ozseccon/ozseccon2019_badge/hw/ozseccon_2019/Badge_2019/gerbers/Production/Validate/prototype-F.SilkS.pdf

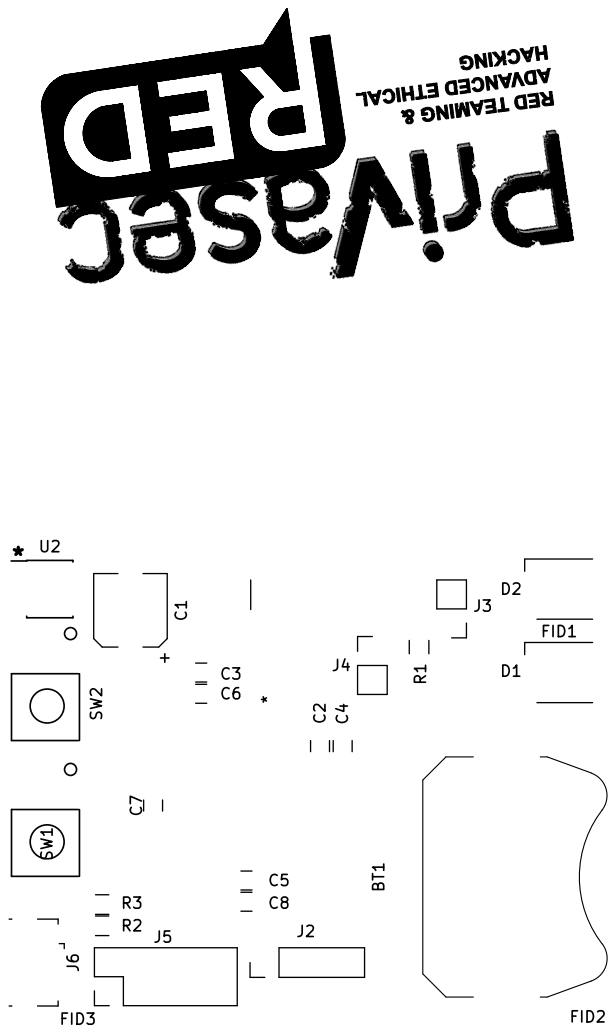
[picture p12: page 1]
