ozseccon/ozseccon2019_badge/hw/ozseccon_2019/Badge_2019/gerbers/Production/Validate/prototype.pdf

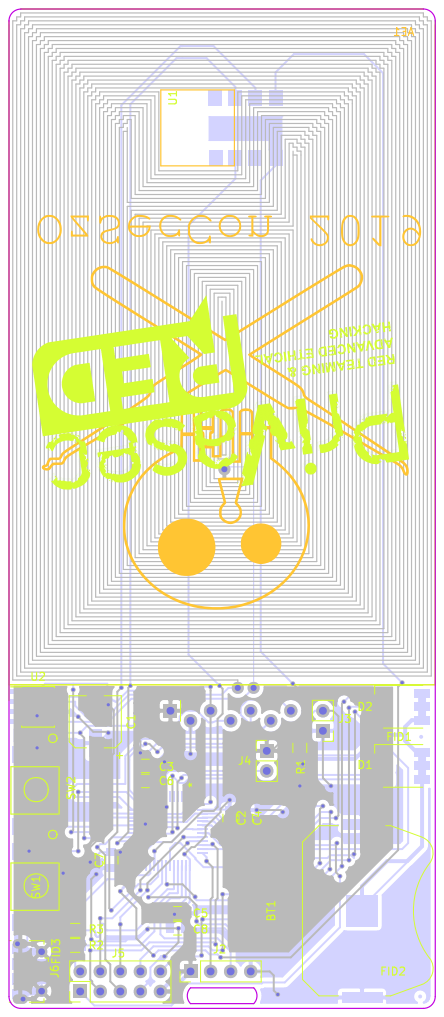
[picture p13: page 1]
