ozseccon/ozseccon2019_badge/hw/ozseccon_2019/Badge_2019/gerbers/Production/Validate/validate.pdf

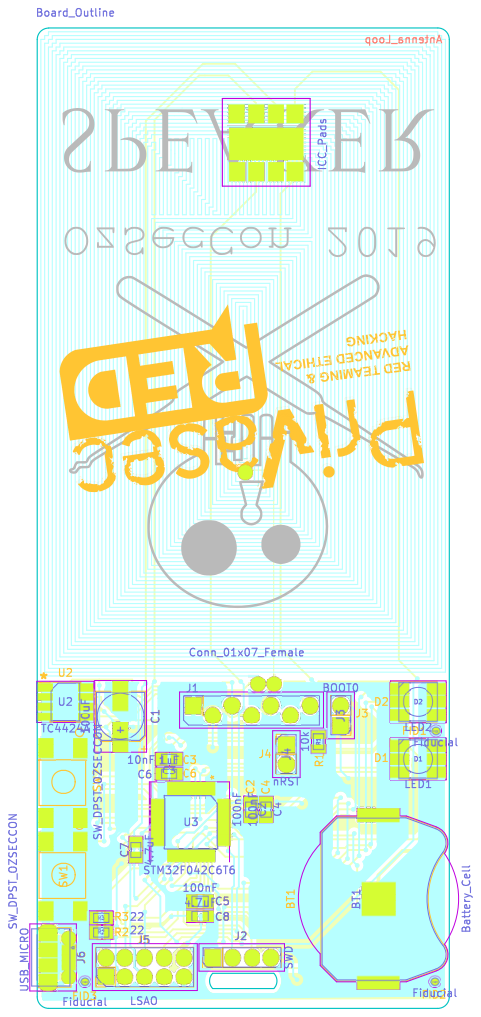
[picture p14: page 1]
