ozseccon/ozseccon2019_badge/hw/ozseccon_2019/Badge_2019/gerbers/svgs/prototype-Edge.Cuts.pdf

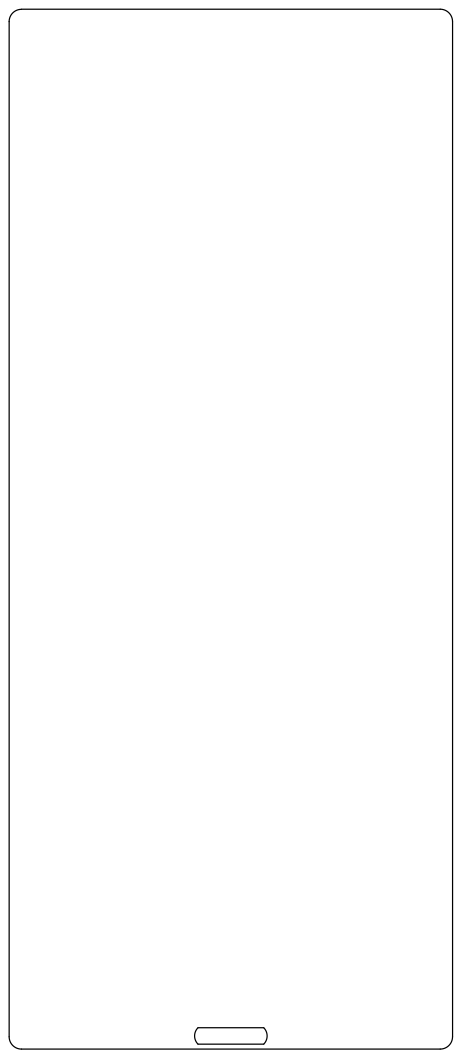
[picture p15: page 1]
