ozseccon/ozseccon2019_badge/hw/ozseccon_2019/Badge_2019/gerbers/svgs/prototype-F.Cu.pdf

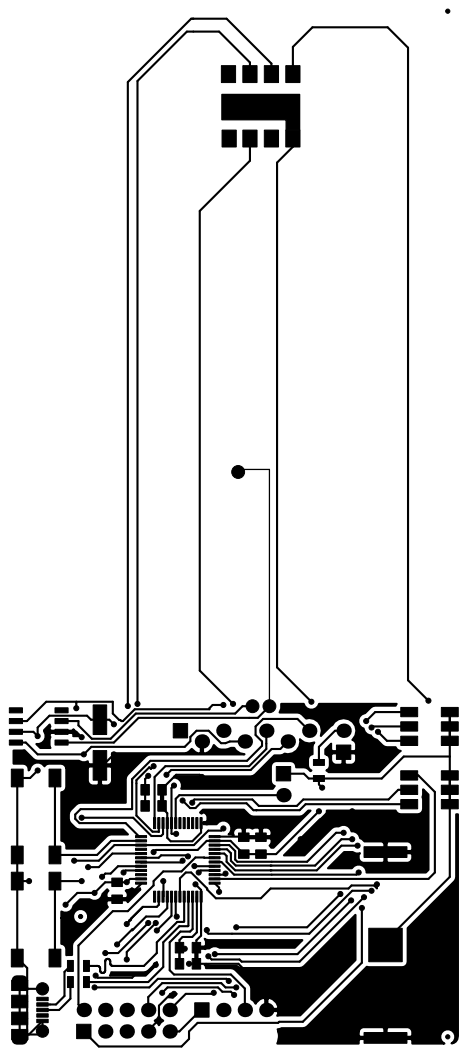
[picture p16: page 1]
