ozseccon/ozseccon2019_badge/hw/ozseccon_2019/Badge_2019/gerbers/svgs/prototype-F.Mask.pdf

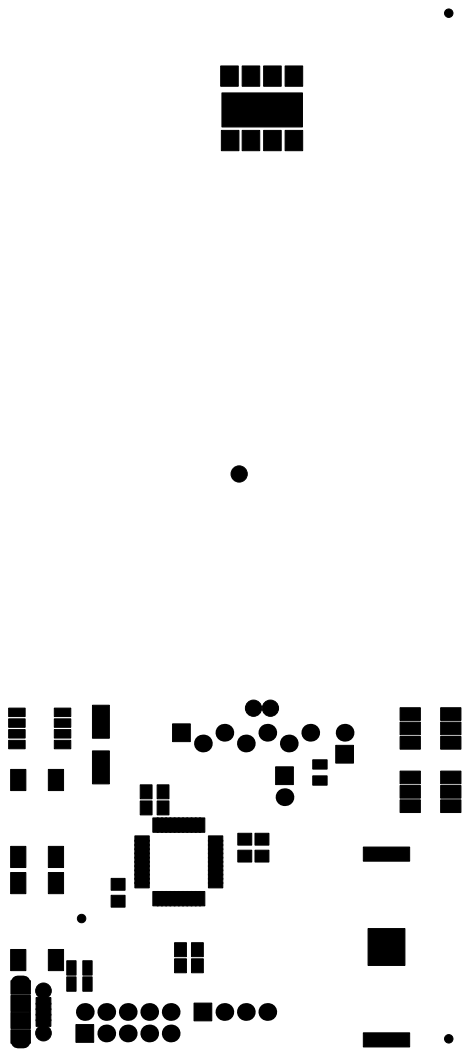
[picture p17: page 1]
