ozseccon/ozseccon2019_badge/hw/ozseccon_2019/Badge_2019/gerbers/svgs/prototype-F.SilkS.pdf

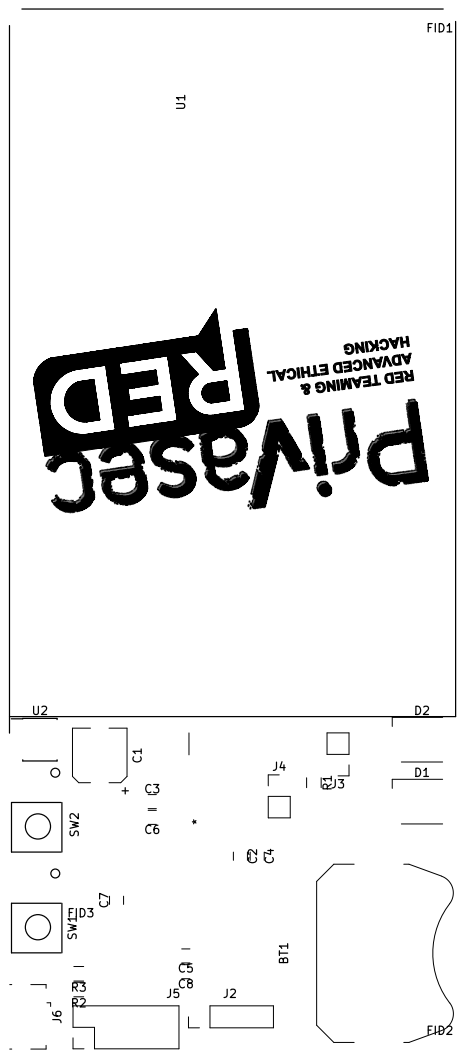
[picture p18: page 1]
