ozseccon/ozseccon2019_badge/hw/ozseccon_2019/Badge_2019/gerbers/Production/Validate/prototype-B.Cu.pdf

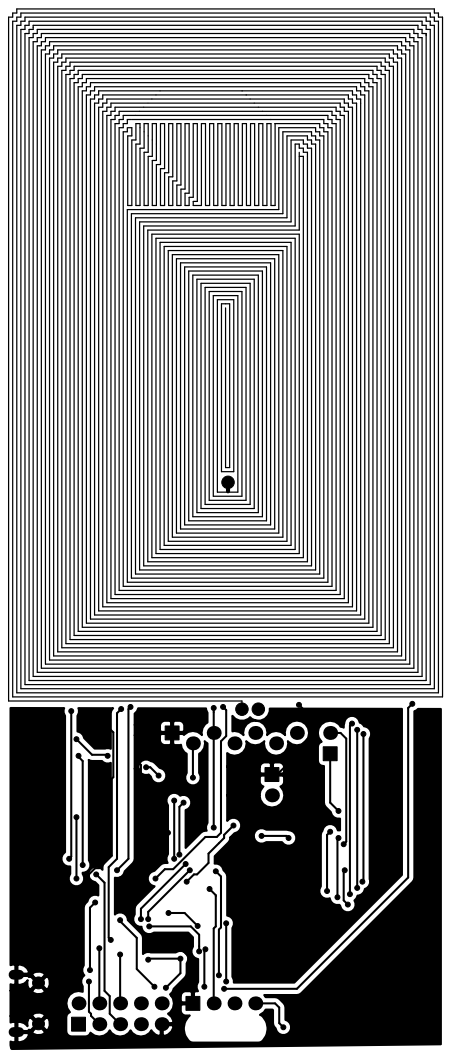
[picture p19: page 1]
