ozseccon/ozseccon2019_badge/hw/ozseccon_2019/Badge_2019/gerbers/Production/Validate/prototype-B.Mask.pdf

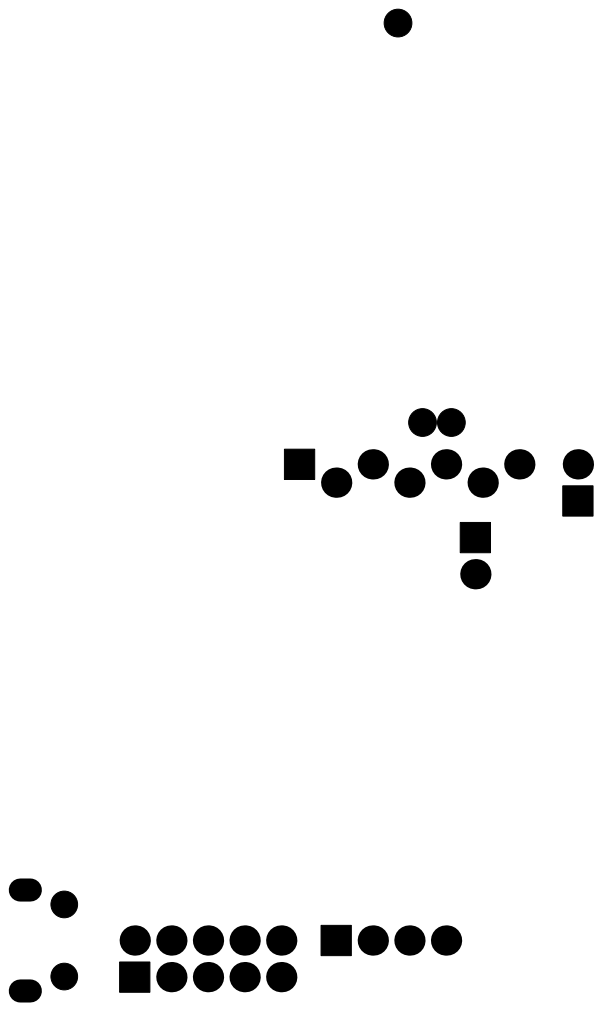
[picture p20: page 1]
