ozseccon/ozseccon2019_badge/hw/ozseccon_2019/Badge_2019/gerbers/Production/Validate/prototype-B.SilkS.pdf

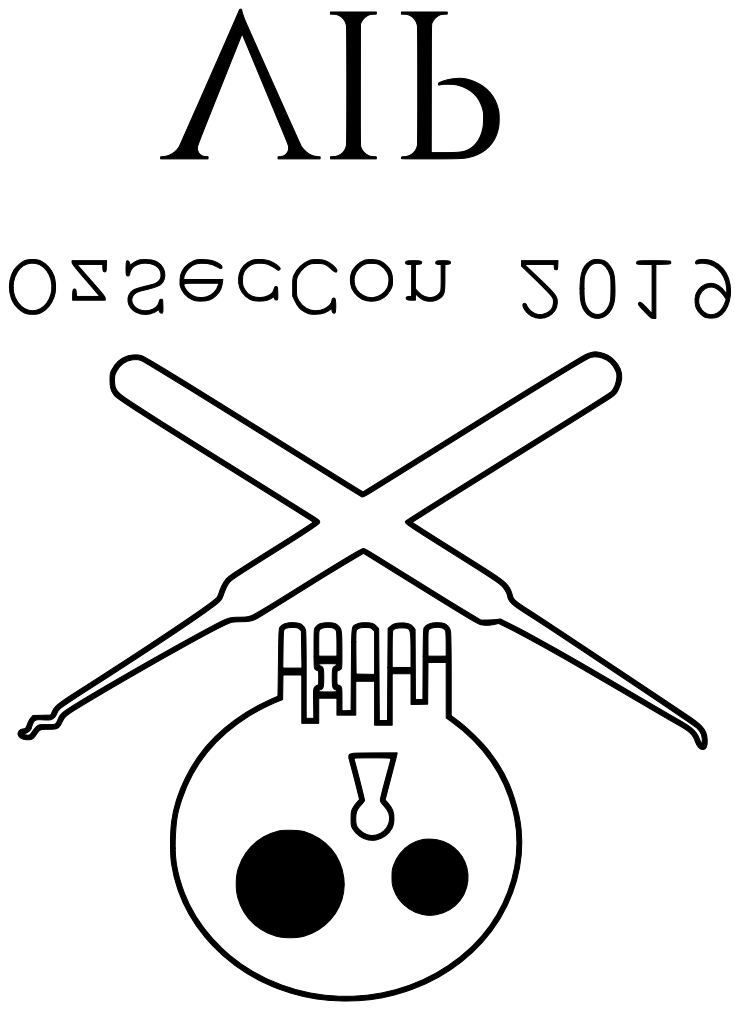
[picture p21: page 1]
