ozseccon/ozseccon2019_badge/hw/ozseccon_2019/Badge_2019/gerbers/svgs/prototype-B.Cu.pdf

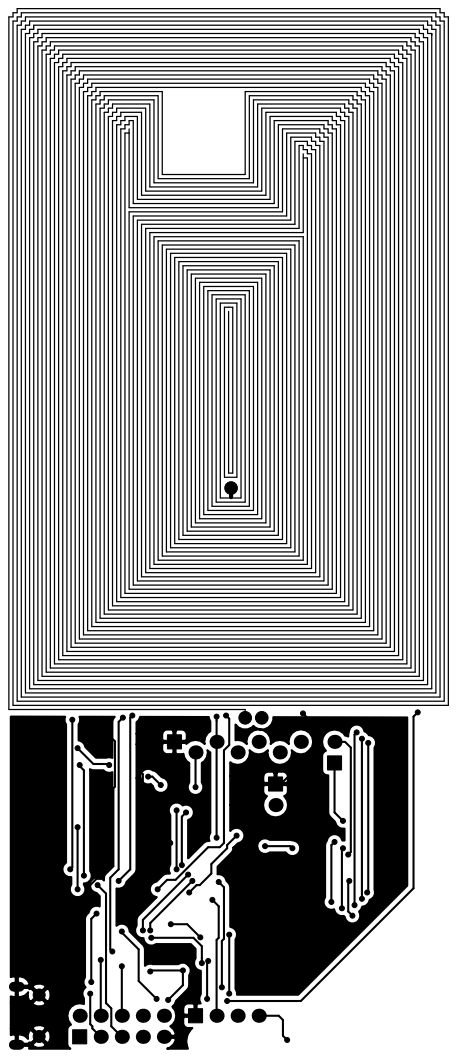
[picture p22: page 1]
