ozseccon/ozseccon2019_badge/hw/ozseccon_2019/Badge_2019/gerbers/svgs/prototype-B.SilkS.pdf

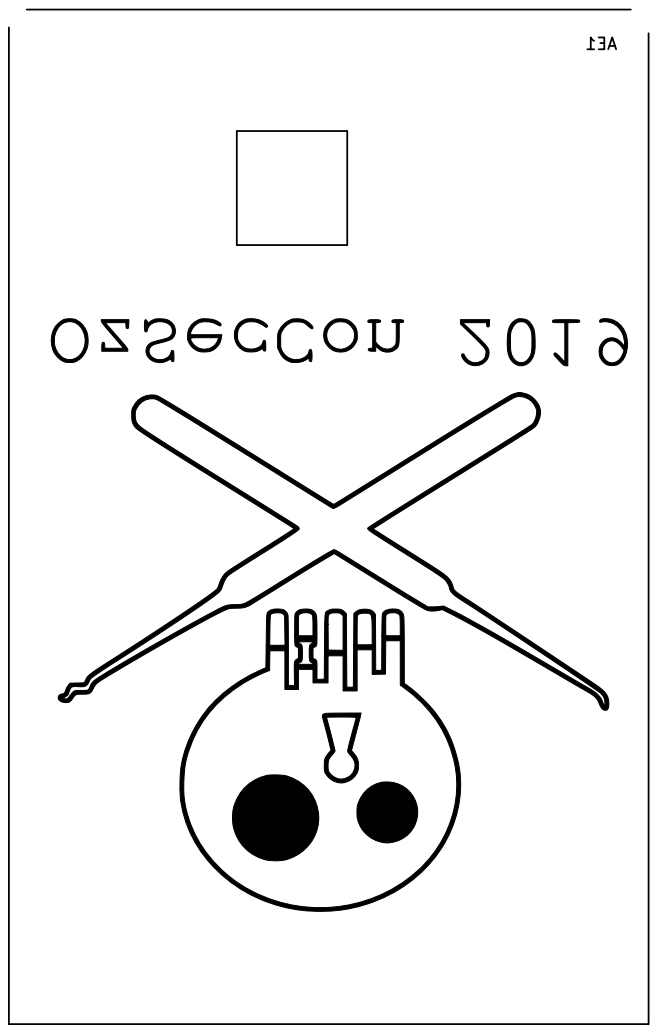
[picture p23: page 1]
