ozseccon/ozseccon2019_badge/hw/ozseccon_2019/Badge_2019/gerbers/Production/Delegate/prototype-B.SilkS.pdf

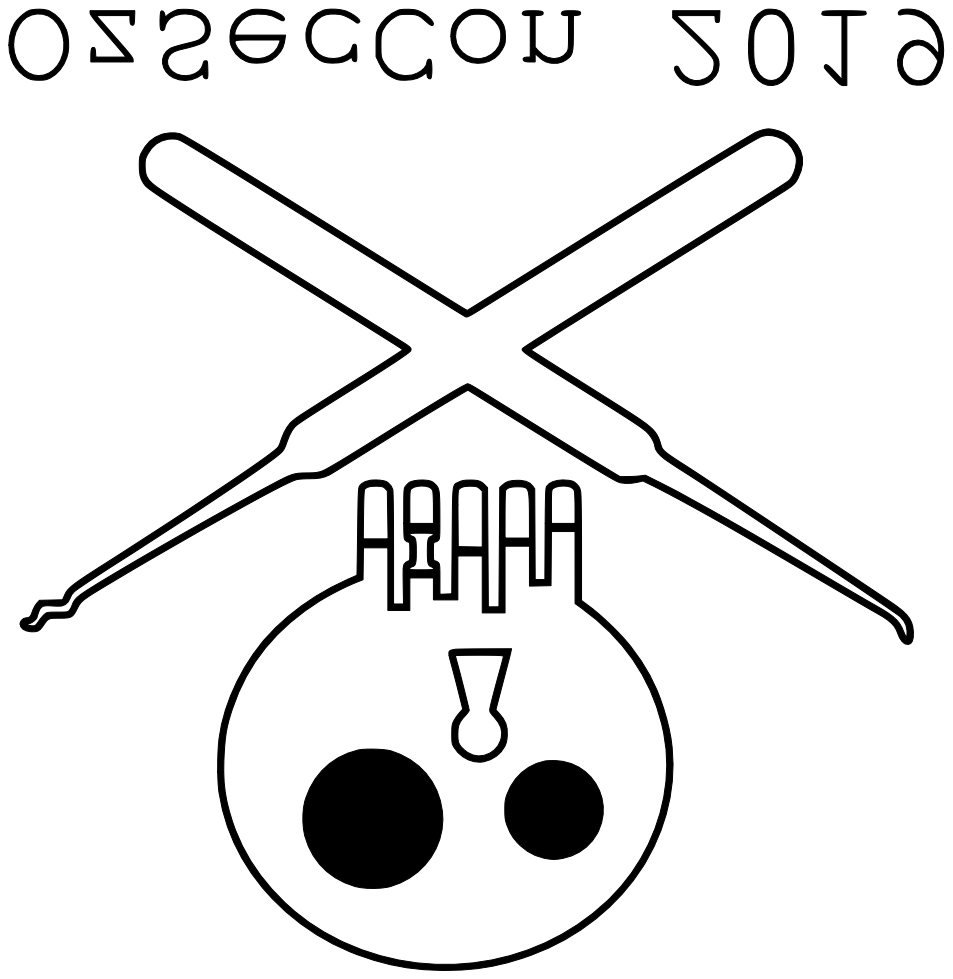
[picture p24: page 1]
