ozseccon/ozseccon2019_badge/hw/ozseccon_2019/Badge_2019/magspoof.sch

## EAGLE design hw/ozseccon_2019/Badge_2019/magspoof.sch (2019-05-05)

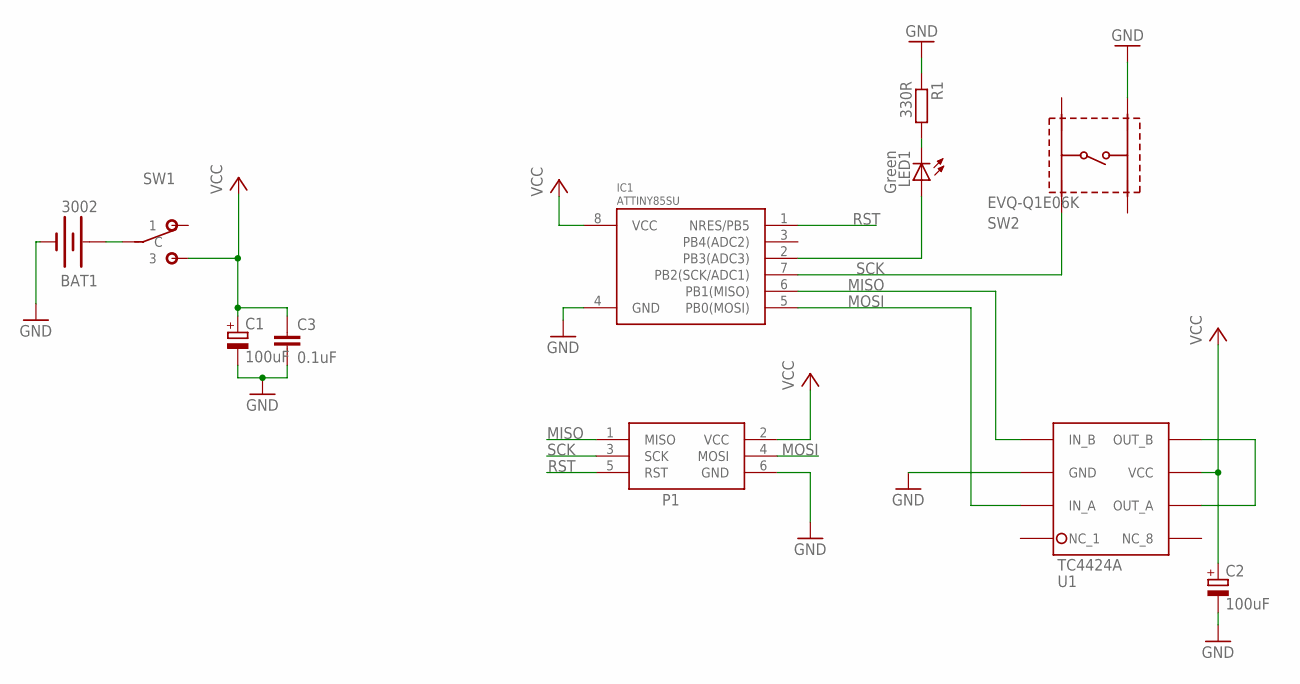
[picture p25: schematic magspoof.sch]

Parts:
BAT1: 3002; BATTCON_20MM
C1, C2: 100uF; C1411
C3: 0.1uF; C0603
IC1: ATTINY85SU; ATTINY85
LED1: Green; CHIPLED_0805
P1: AVRISP-6; AVRISP
R1: 330R; R0603
SW1: JS102011; JS102011SAQN
SW2: EVQ-Q1E06K; EVQQ1
U1: TC4424A; 8-SOIC

Connections:
ANTENNA: U1.5 (OUT_B), U1.7 (OUT_A)
GND: BAT1.-, C1.P$2 (-), C2.P$2 (-), C3.2, IC1.4 (GND), P1.6 (GND), R1.1, SW2.D, U1.3 (GND)
MISO: IC1.6 (PB1(MISO)), P1.1 (MISO), U1.4 (IN_B)
MOSI: IC1.5 (PB0(MOSI)), P1.4 (MOSI), U1.2 (IN_A)
unnamed: BAT1.+2 (+), SW1.P$2 (C)
unnamed: IC1.2 (PB3(ADC3)), LED1.A
unnamed: LED1.C, R1.2
RST: IC1.1 (NRES/PB5), P1.5 (RST)
SCK: IC1.7 (PB2(SCK/ADC1)), P1.3 (SCK), SW2.A
VCC: C1.P$1 (+), C2.P$1 (+), C3.1, IC1.8 (VCC), P1.2 (VCC), SW1.P$3 (3), U1.6 (VCC)
