ozseccon/ozseccon2019_badge/hw/ozseccon_2019/Badge_2019/microcontroller.sch

## KiCad design hw/ozseccon_2019/Badge_2019/microcontroller.sch (2019-05-05)

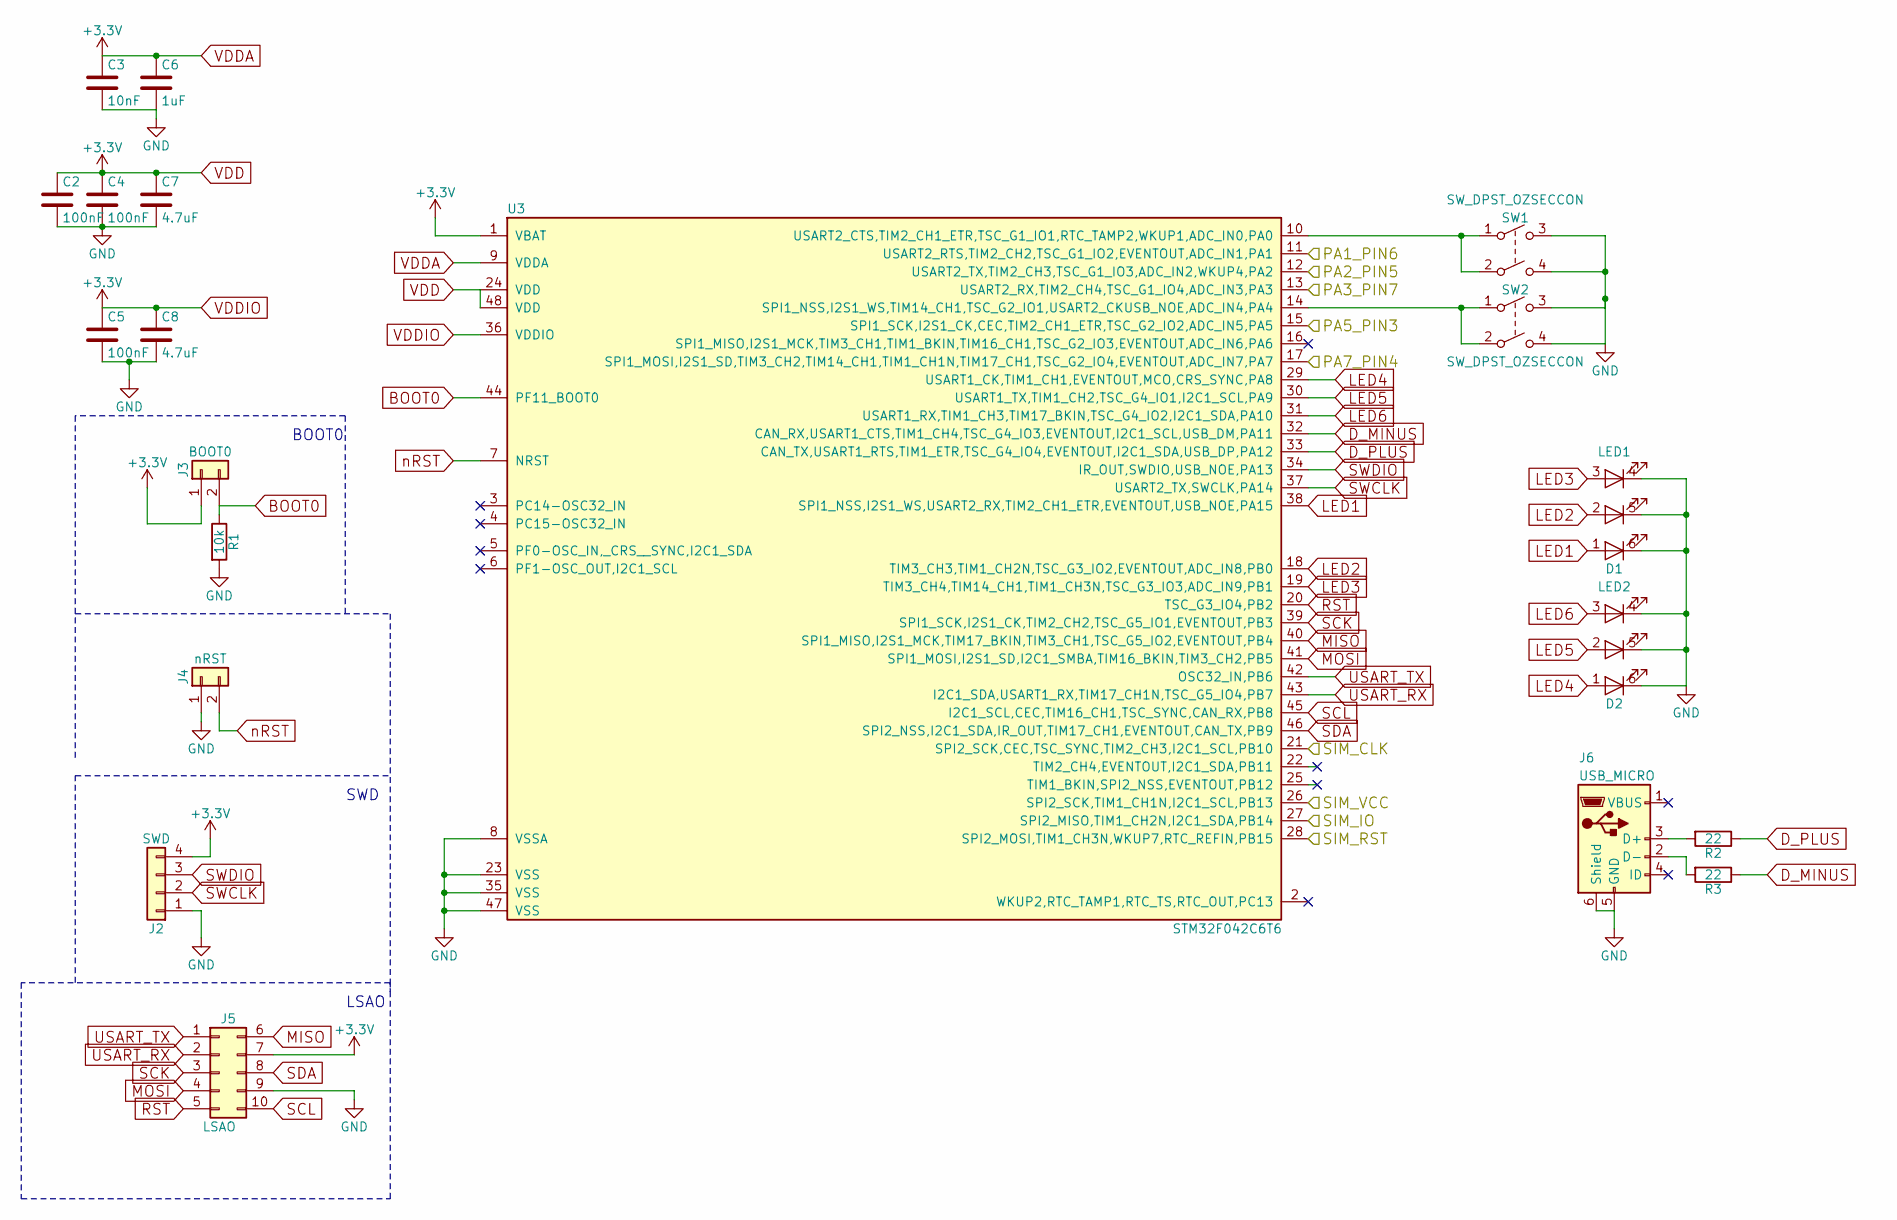
[picture p26: schematic microcontroller.sch]

Parts:
C2, C4, C5: 100nF; C_0805
C3: 10nF; C_0805
C6: 1uF; C_0805
C7, C8: 4.7uF; C_0805
D1: LED1; LED_RGB_5050-6
D2: LED2; LED_RGB_5050-6
J2: SWD; Pin_Header_Straight_1x04_Pitch2.54mm
J3: BOOT0; Pin_Header_Straight_1x02_Pitch2.54mm
J4: nRST; Pin_Header_Straight_1x02_Pitch2.54mm
J5: LSAO; Pin_Header_Straight_2x05_Pitch2.54mm
J6: USB_MICRO; USB_Micro-B_Molex-105017-0001
R1: 10k; R_0805
R2, R3: 22; R_0805
SW1, SW2: SW_DPST_OZSECCON; TactSwitch
U3: STM32F042C6T6; OzSecCon_LQFP-48_7x7mm_Pitch0.5mm

Connections:
+3.3V: C2.1, C3.1, C4.1, C5.1, C6.1, C7.1, C8.1, J2.4, J3.1, J5.7, U3.1 (VBAT), U3.9 (VDDA), U3.24 (VDD), U3.36 (VDDIO), U3.48 (VDD)
BOOT0: J3.2, R1.1, U3.44 (PF11_BOOT0)
D_MINUS: R3.1, U3.32 (CAN_RX,USART1_CTS,TIM1_CH4,TSC_G4_IO3,E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)
D_PLUS: R2.1, U3.33 (CAN_TX,USART1_RTS,TIM1_ETR,TSC_G4_IO4,E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)
GND: C2.2, C3.2, C4.2, C5.2, C6.2, C7.2, C8.2, D1.4 (K_GREEN), D1.5 (K_RED), D1.6 (K_BLUE), D2.4 (K_GREEN), D2.5 (K_RED), D2.6 (K_BLUE), J2.1, J4.1, J5.9, J6.5 (GND), J6.6 (Shield), R1.2, SW1.3, SW1.4, SW2.3, SW2.4, U3.8 (VSSA), U3.23 (VSS), U3.35 (VSS), U3.47 (VSS)
LED1: D1.1 (BLUE_A), U3.38 (SPI1_NSS,I2S1_WS,USART2_RX,TIM2_CH1_ETR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)
LED2: D1.2 (A_RED), U3.18 (TIM3_CH3,TIM1_CH2N,TSC_G3_IO2,EVENTOUT,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)
LED3: D1.3 (GREEN_A), U3.19 (TIM3_CH4,TIM14_CH1,TIM1_CH3N,TSC_G3_IO3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)
LED4: D2.1 (BLUE_A), U3.29 (USART1_CK,TIM1_CH1,EVENTOUT,MCO,CRS_SYN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)
LED5: D2.2 (A_RED), U3.30 (USART1_TX,TIM1_CH2,TSC_G4_IO1,I2C1_SCL,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)
LED6: D2.3 (GREEN_A), U3.31 (USART1_RX,TIM1_CH3,TIM17_BKIN,TSC_G4_IO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)
MISO: J5.6, U3.40 (SPI1_MISO,I2S1_MCK,TIM17_BKIN,TIM3_CH1,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)
MOSI: J5.4, U3.41 (SPI1_MOSI,I2S1_SD,I2C1_SMBA,TIM16_BKIN,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)
unnamed: J6.2 (D-), R3.2
unnamed: J6.3 (D+), R2.2
unnamed: SW1.1, SW1.2, U3.10 (USART2_CTS,TIM2_CH1_ETR,TSC_G1_IO1,RTC_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)
unnamed: SW2.1, SW2.2, U3.14 (SPI1_NSS,I2S1_WS,TIM14_CH1,TSC_G2_IO1,U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)
PA1_PIN6: U3.11 (USART2_RTS,TIM2_CH2,TSC_G1_IO2,EVENTOUT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)
PA2_PIN5: U3.12 (USART2_TX,TIM2_CH3,TSC_G1_IO3,ADC_IN2,W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)
PA3_PIN7: U3.13 (USART2_RX,TIM2_CH4,TSC_G1_IO4,ADC_IN3,P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)
PA5_PIN3: U3.15 (SPI1_SCK,I2S1_CK,CEC,TIM2_CH1_ETR,TSC_G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)
PA7_PIN4: U3.17 (SPI1_MOSI,I2S1_SD,TIM3_CH2,TIM14_CH1,TI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)
RST: J5.5, U3.20 (TSC_G3_IO4,PB2)
SCK: J5.3, U3.39 (SPI1_SCK,I2S1_CK,TIM2_CH2,TSC_G5_IO1,EV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)
SCL: J5.10, U3.45 (I2C1_SCL,CEC,TIM16_CH1,TSC_SYNC,CAN_RX,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)
SDA: J5.8, U3.46 (SPI2_NSS,I2C1_SDA,IR_OUT,TIM17_CH1,EVEN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)
SIM_CLK: U3.21 (SPI2_SCK,CEC,TSC_SYNC,TIM2_CH3,I2C1_SCL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)
SIM_IO: U3.27 (SPI2_MISO,TIM1_CH2N,I2C1_SDA,PB14)
SIM_RST: U3.28 (SPI2_MOSI,TIM1_CH3N,WKUP7,RTC_REFIN,PB15)
SIM_VCC: U3.26 (SPI2_SCK,TIM1_CH1N,I2C1_SCL,PB13)
SWCLK: J2.2, U3.37 (USART2_TX,SWCLK,PA14)
SWDIO: J2.3, U3.34 (IR_OUT,SWDIO,USB_NOE,PA13)
USART_RX: J5.2, U3.43 (I2C1_SDA,USART1_RX,TIM17_CH1N,TSC_G5_IO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)
USART_TX: J5.1, U3.42 (OSC32_IN,PB6)
nRST: J4.2, U3.7 (NRST)

Notes on the sheet:
LSAO
SWD
BOOT0
