ozseccon/ozseccon2019_badge/hw/ozseccon_2019/Badge_2019/prototype.sch

## KiCad design hw/ozseccon_2019/Badge_2019/prototype.sch (2019-05-05)

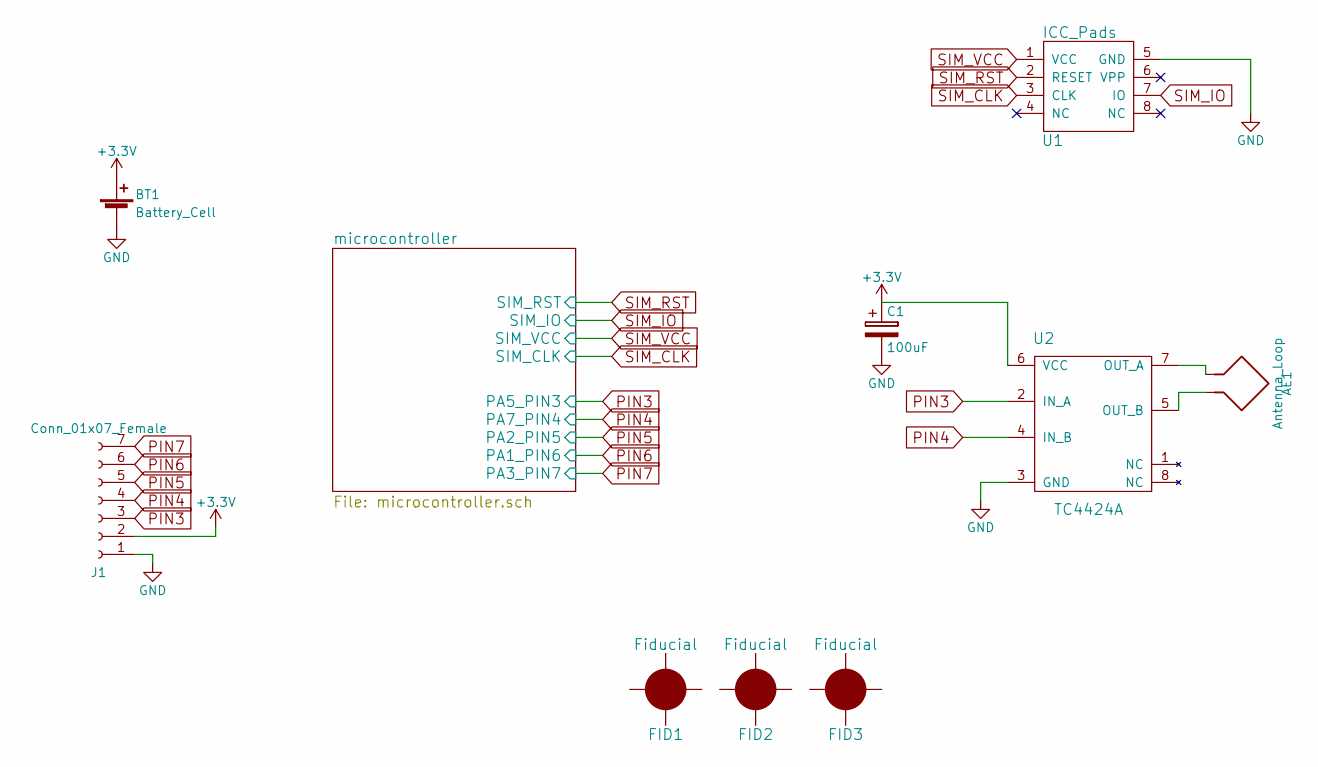
[picture p27: schematic prototype.sch]

Parts:
AE1: Antenna_Loop; Antenna
BT1: Battery_Cell; Keystone_3034_1x20mm-CoinCell
C1: 100uF; CP_Elec_6.3x5.7
FID1, FID2, FID3: Fiducial; Fiducial_Modern_CopperTop
J1: Conn_01x07_Female; BoldPort_Pin_Header_Straight_1x07_Pitch2.54mm
U1: ICC_Pads; ICC_FOOTPRINT
U2: TC4424A; SOIC-8_3.9x4.9mm_Pitch1.27mm

Connections:
+3.3V: BT1.1 (+), C1.1, J1.2, U2.6 (VCC)
GND: BT1.2 (-), C1.2, J1.1, U1.5 (GND), U2.3 (GND)
unnamed: AE1.1, U2.7 (OUT_A)
unnamed: AE1.2, U2.5 (OUT_B)
PIN3: J1.3, U2.2 (IN_A)
PIN4: J1.4, U2.4 (IN_B)
PIN5: J1.5
PIN6: J1.6
PIN7: J1.7
SIM_CLK: U1.3 (CLK)
SIM_IO: U1.7 (IO)
SIM_RST: U1.2 (RESET)
SIM_VCC: U1.1 (VCC)
