ozseccon/ozseccon2019_badge/fw/src/config.rs

pub const CLOCK_SPEED: u32 = 8_000_000;
pub const DEVICE_VID: u16 = 0xffff;
pub const DEVICE_PID: u16 = 0xffff;

#[cfg(test)]
mod tests {
    use super::CLOCK_SPEED;

    #[test]
    fn correct_clock_speed() {
        assert_eq!(CLOCK_SPEED, 8_000_000);
    }
}
